innovationgarage/WibblyWobbly/firmware/MotionRecorder/I2C.ino

void I2C_Write(uint8_t deviceAddress, uint8_t regAddress, uint8_t data) {
  Wire.beginTransmission(deviceAddress);
  Wire.write(regAddress);
  Wire.write(data);
  Wire.endTransmission();
}

// read all 14 register
void Read_RawValue(uint8_t deviceAddress, uint8_t regAddress) {
  Wire.beginTransmission(deviceAddress);
  Wire.write(regAddress);
  Wire.endTransmission();
  Wire.requestFrom(deviceAddress, (uint8_t)14);
  AccelX = (((int16_t)Wire.read() << 8) | Wire.read());
  AccelY = (((int16_t)Wire.read() << 8) | Wire.read());
  AccelZ = (((int16_t)Wire.read() << 8) | Wire.read());
  Temperature = (((int16_t)Wire.read() << 8) | Wire.read());
  GyroX = (((int16_t)Wire.read() << 8) | Wire.read());
  GyroY = (((int16_t)Wire.read() << 8) | Wire.read());
  GyroZ = (((int16_t)Wire.read() << 8) | Wire.read());
}

//configure MPU6050
void MPU6050_Init() {
  delay(150);
  I2C_Write(MPU6050SlaveAddress, MPU6050_REGISTER_SMPLRT_DIV, 0x07);
  I2C_Write(MPU6050SlaveAddress, MPU6050_REGISTER_PWR_MGMT_1, 0x01);
  I2C_Write(MPU6050SlaveAddress, MPU6050_REGISTER_PWR_MGMT_2, 0x00);
  I2C_Write(MPU6050SlaveAddress, MPU6050_REGISTER_CONFIG, 0x00);
  I2C_Write(MPU6050SlaveAddress, MPU6050_REGISTER_GYRO_CONFIG, 0x00);//set +/-250 degree/second full scale
  I2C_Write(MPU6050SlaveAddress, MPU6050_REGISTER_ACCEL_CONFIG, 0x00);// set +/- 2g full scale
  I2C_Write(MPU6050SlaveAddress, MPU6050_REGISTER_FIFO_EN, 0x00);
  I2C_Write(MPU6050SlaveAddress, MPU6050_REGISTER_INT_ENABLE, 0x01);
  I2C_Write(MPU6050SlaveAddress, MPU6050_REGISTER_SIGNAL_PATH_RESET, 0x00);
  I2C_Write(MPU6050SlaveAddress, MPU6050_REGISTER_USER_CTRL, 0x00);
}
